dekuNukem/ATX4VC/photos/begin.png

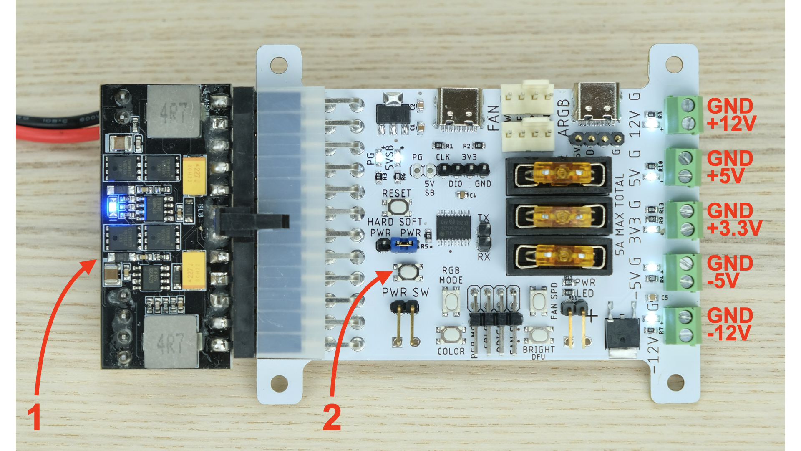
photos/begin.png
