dekuNukem/ATX4VC/photos/coffee.jpeg

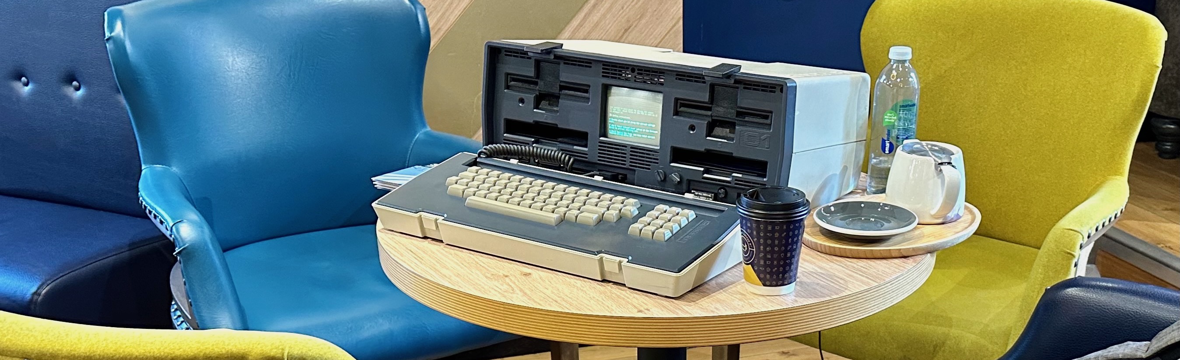
photos/coffee.jpeg
