dekuNukem/ATX4VC/photos/fuse.png

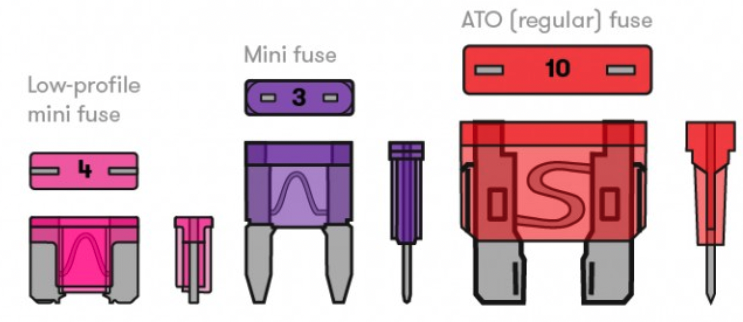
photos/fuse.png
