dekuNukem/ATX4VC/photos/fuses.jpeg

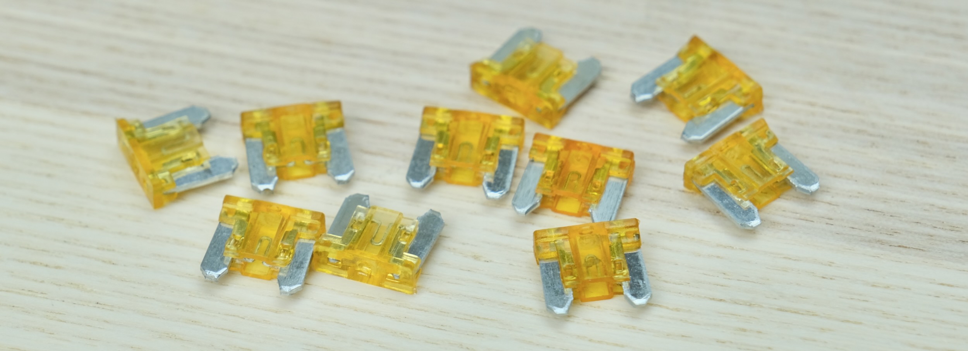
photos/fuses.jpeg
