dekuNukem/ATX4VC/photos/harness.jpeg

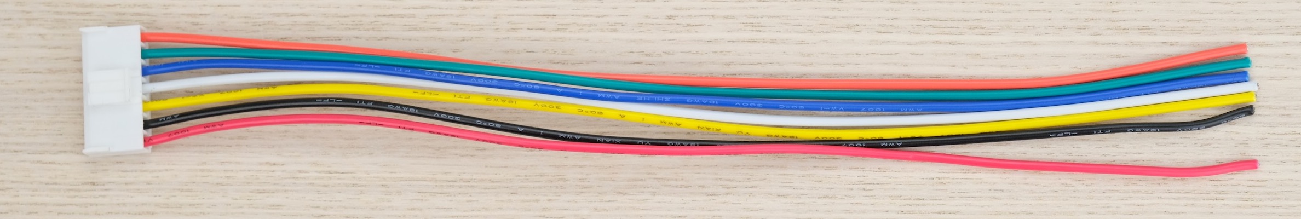
photos/harness.jpeg
