dekuNukem/ATX4VC/photos/jump.png

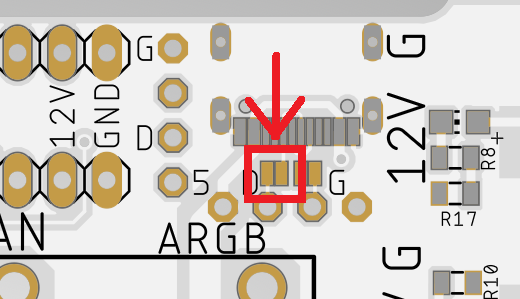
photos/jump.png
