dekuNukem/ATX4VC/photos/legend.png

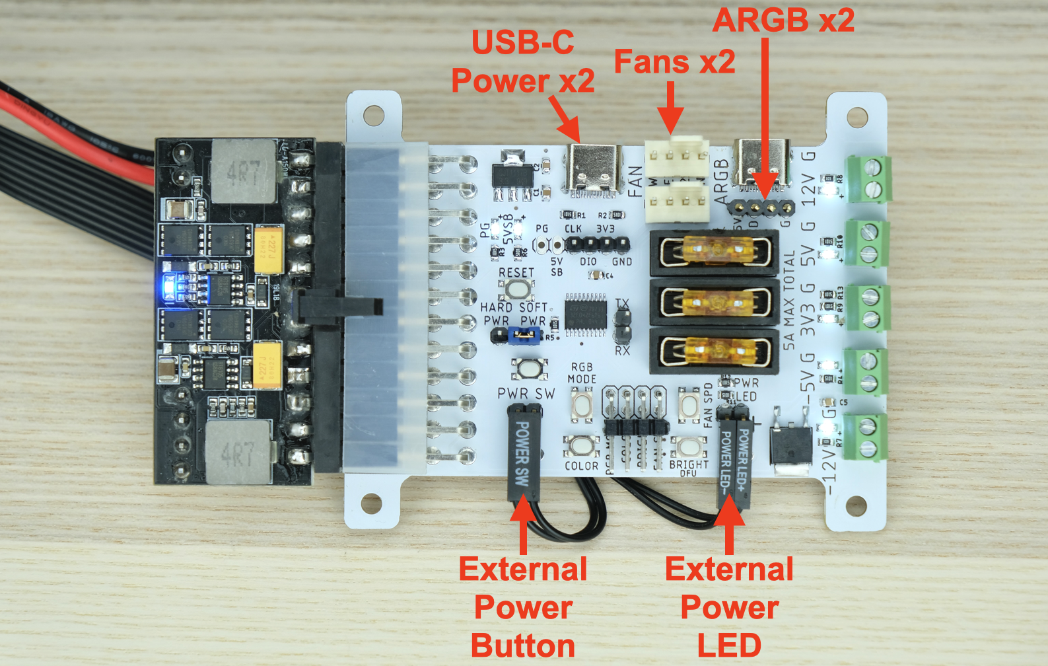
photos/legend.png
