dekuNukem/ATX4VC/photos/lock.jpeg

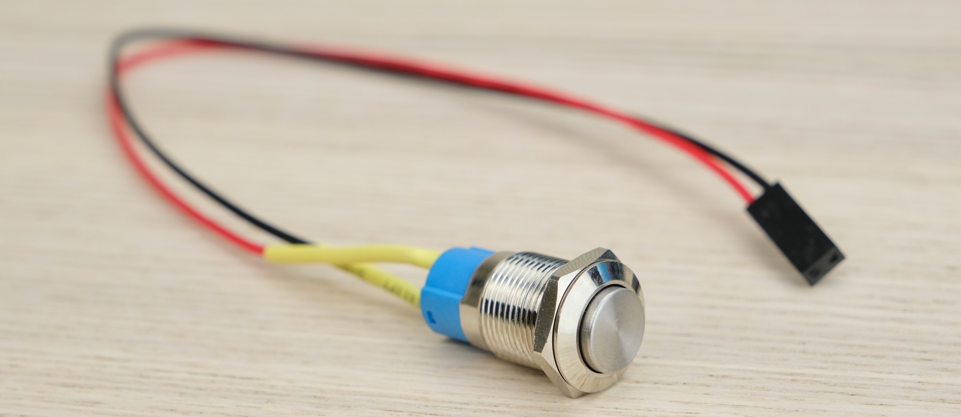
photos/lock.jpeg
