dekuNukem/ATX4VC/photos/mcu.jpeg

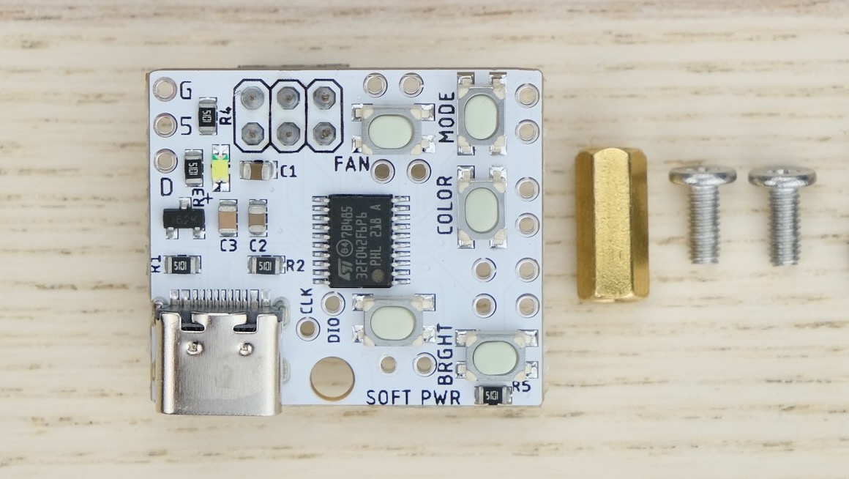
photos/mcu.jpeg
