dekuNukem/ATX4VC/photos/plug.jpeg

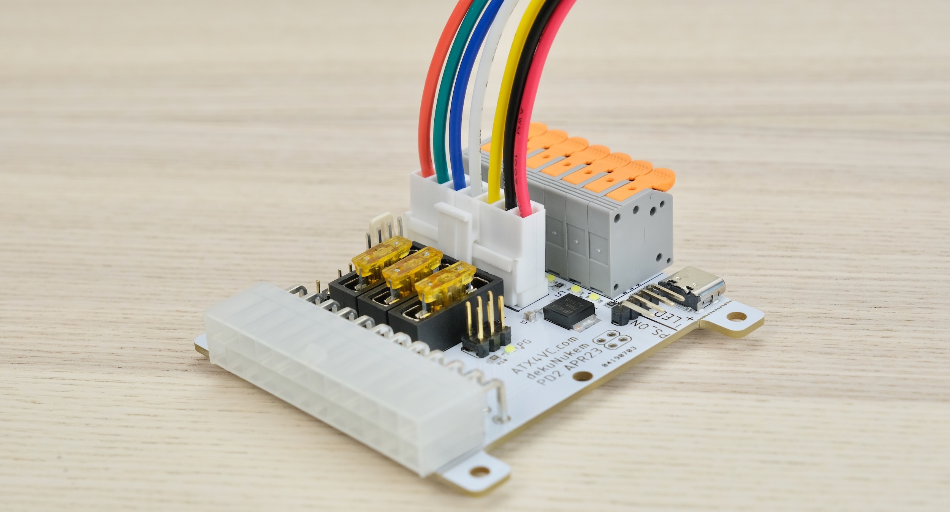
photos/plug.jpeg
