dekuNukem/ATX4VC/photos/switches.jpeg

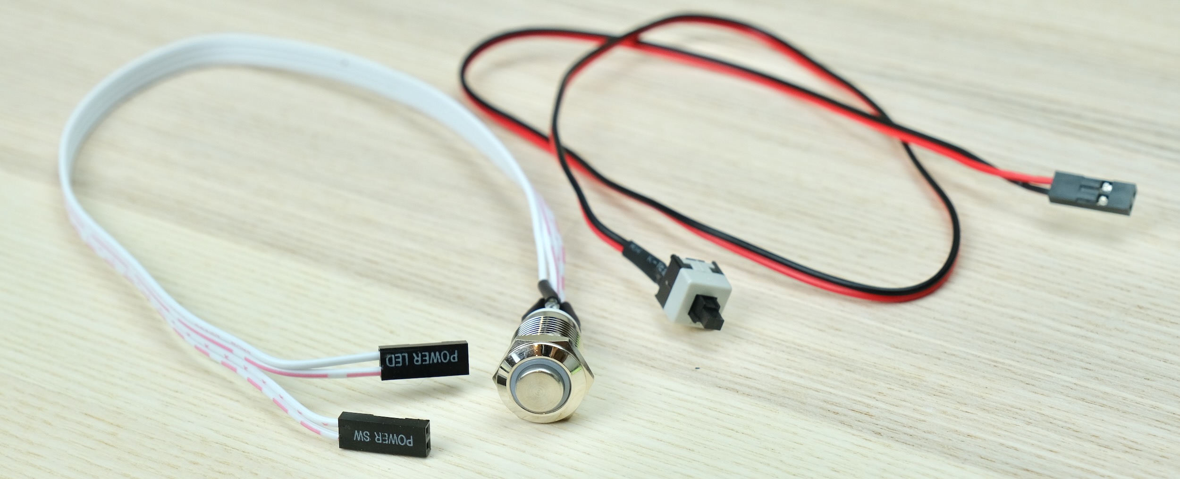
photos/switches.jpeg
