dekuNukem/ATX4VC/resources/newatx4vc.png

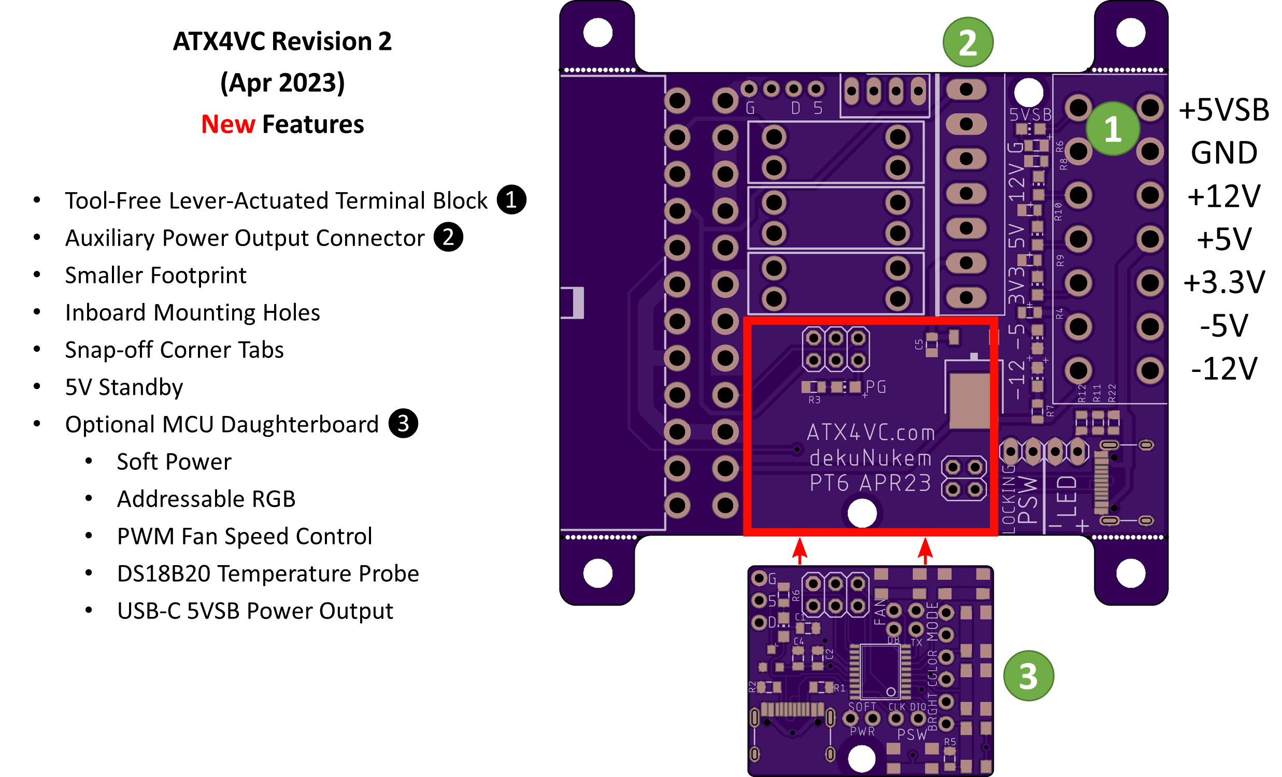
resources/newatx4vc.png
