dekuNukem/ATX4VC/resources/sparkfun_motor_driver/SparkFun_Qwiic_Motor_Driver.brd

## EAGLE design resources/sparkfun_motor_driver/SparkFun_Qwiic_Motor_Driver.brd (2022-07-18)

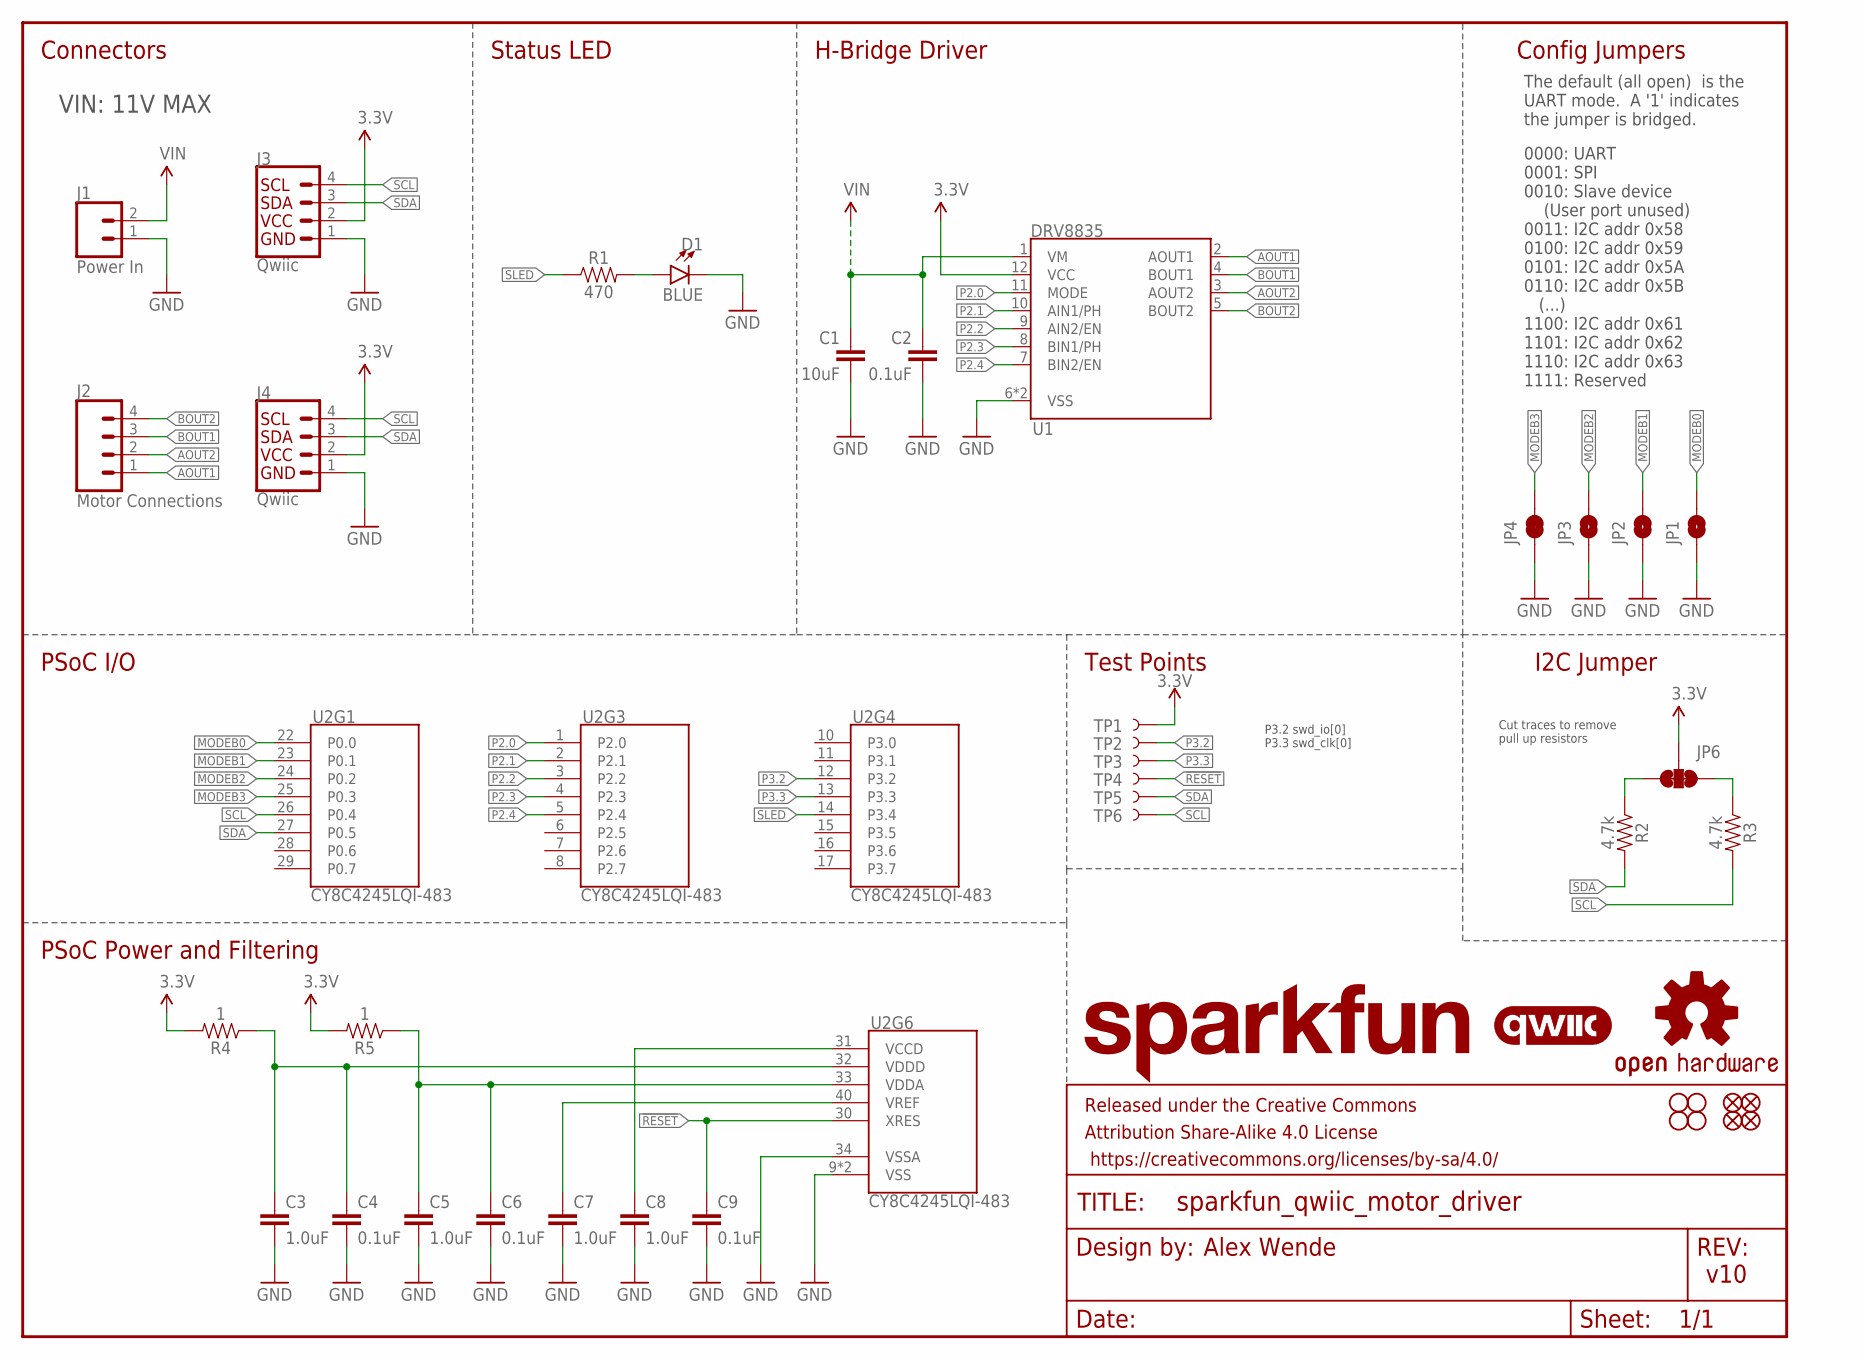
[picture p78: schematic SparkFun_Qwiic_Motor_Driver.sch]

Parts:
C1: 10uF; 0805
C2, C4, C6, C9: 0.1uF; 0402
C3, C5, C7, C8: 1.0uF; 0402
D1: BLUE; LED-0603
FD1, FD2, FD3, FD4: FIDUCIALUFIDUCIAL; FIDUCIAL-MICRO
FRAME1: FRAME-LETTER; CREATIVE_COMMONS
H1, H2, H3, H4: STAND-OFF
J1: Power In; SCREWTERMINAL-3.5MM-2
J2: Motor Connections; SCREWTERMINAL-3.5MM-4
J3, J4: Qwiic; JST04_1MM_RA
JP1, JP2, JP3: JUMPER-PAD-2; SMT-JUMPER_2_NO_NO-SILK
JP4: JUMPER-PAD-2; SMT-JUMPER_2_NC_TRACE_NO-SILK
JP6: JUMPER-SMT_3_2-NC_TRACE_NO-SILK; SMT-JUMPER_3_2-NC_TRACE_NO-SILK
LOGO2: OSHW-LOGOMINI; OSHW-LOGO-MINI
LOGO3: SFE_LOGO_NAME.1_INCH; SFE_LOGO_NAME_.1
R1: 470; 0603
R2, R3: 4.7k; 0603
R4, R5: 1; 0603
TP1, TP2, TP3, TP4, TP5, TP6: TEST-POINTTP_15TH_THRU; TP_15TH
U1: DRV8835; WSON-12
U2: CY8C4245LQI-483; QFN-40
U$1: QWIIC_LOGO_5MM; QWIIC_5MM

Connections:
3.3V: J3.2, J4.2, JP6.2, R4.2, R5.2, TP1.P$1, U1.12 (VCC)
!RESET: C9.1, TP4.P$1, U2.30 (XRES)
AOUT1: J2.1, U1.2 (AOUT1)
AOUT2: J2.2, U1.3 (AOUT2)
BOUT1: J2.3, U1.4 (BOUT1)
BOUT2: J2.4, U1.5 (BOUT2)
GND: C1.2, C2.2, C3.2, C4.2, C5.2, C6.2, C7.2, C8.2, C9.2, D1.C, J1.1, J3.1, J4.1, JP1.1, JP2.1, JP3.1, JP4.1, U1.6 (VSS), U1.PAD (VSS), U2.9 (VSS), U2.34 (VSSA), U2.EP (VSS)
MODEB0: JP1.2, U2.22 (P0.0)
MODEB1: JP2.2, U2.23 (P0.1)
MODEB2: JP3.2, U2.24 (P0.2)
MODEB3: JP4.2, U2.25 (P0.3)
unnamed: C8.1, U2.31 (VCCD)
unnamed: C5.1, C6.1, R5.1, U2.33 (VDDA)
unnamed: C7.1, U2.40 (VREF)
unnamed: D1.A, R1.2
unnamed: JP6.1, R3.1
unnamed: JP6.3, R2.1
P2.0: U1.11 (MODE), U2.1 (P2.0)
P2.1: U1.10 (AIN1/PH), U2.2 (P2.1)
P2.2: U1.9 (AIN2/EN), U2.3 (P2.2)
P2.3: U1.8 (BIN1/PH), U2.4 (P2.3)
P2.4: U1.7 (BIN2/EN), U2.5 (P2.4)
P3.2: TP2.P$1, U2.12 (P3.2)
P3.3: TP3.P$1, U2.13 (P3.3)
SCL: J3.4, J4.4, R3.2, TP6.P$1, U2.26 (P0.4)
SDA: J3.3, J4.3, R2.2, TP5.P$1, U2.27 (P0.5)
SLED: R1.1, U2.14 (P3.4)
VDDD: C3.1, C4.1, R4.1, U2.32 (VDDD)
VIN: C1.1, C2.1, J1.2, U1.1 (VM)

Notes on the sheet:
PSoC Power and Filtering
Config Jumpers
Alex Wende
PSoC I/O
v10
P3.2 swd_io[0] P3.3 swd_clk[0]
0000: UART 0001: SPI 0010: Slave device (User port unused) 0011: I2C addr 0x58 0100: I2C addr 0x59 0101: I2C addr 0x5A 0110: I2C addr 0x5B (...) 1100: I2C addr 0x61 1101: I2C addr 0x62 1110: I2C addr 0x63 1111: Reserved
The default (all open) is the UART mode. A '1' indicates the jumper is bridged.
Connectors
Status LED
H-Bridge Driver
Test Points
I2C Jumper
VIN: 11V MAX
Cut traces to remove pull up resistors

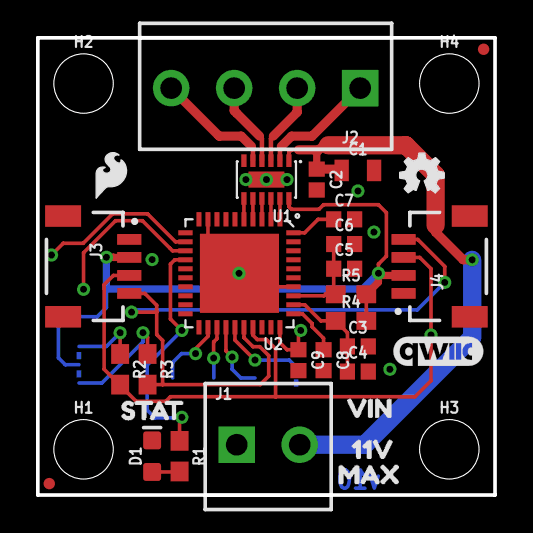
[picture p79: board SparkFun_Qwiic_Motor_Driver.brd from above]

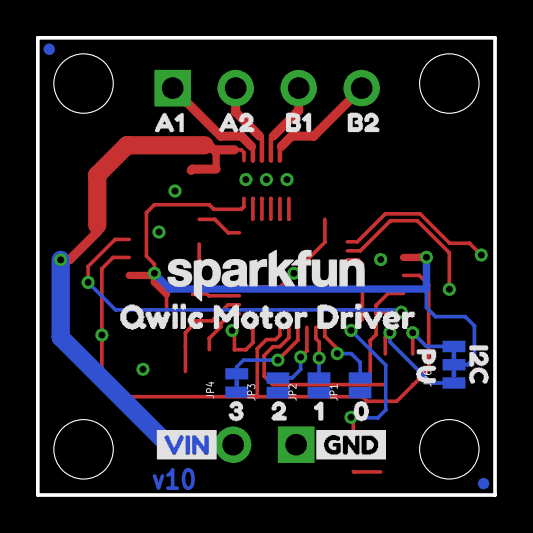
[picture p80: board SparkFun_Qwiic_Motor_Driver.brd from below]

Board: 2 copper layers, 25.4 x 25.4 mm, 62 parts (21 on the bottom side), 29 nets.

Other parts of the board:
U$2: STAT4
U$3: GND3
U$4: VIN2
U$5: 05
U$6: 16
U$7: 27
U$8: 38
U$9: A110
U$10: A211
U$11: B112
U$12: B213
U$13: 11V7
U$14: MAX8
U$15: VIN6
U$16: I2C0
U$17: PU1
U$18: QWIIC_MOTOR_DRIVER0
U$19: SFE_LOGO_FLAME_.1
