dekuNukem/ATX4VC/resources/sparkfun_atx/Benchtop Power Supply-v13.brd

## EAGLE design resources/sparkfun_atx/Benchtop Power Supply-v13.brd (2022-07-18)

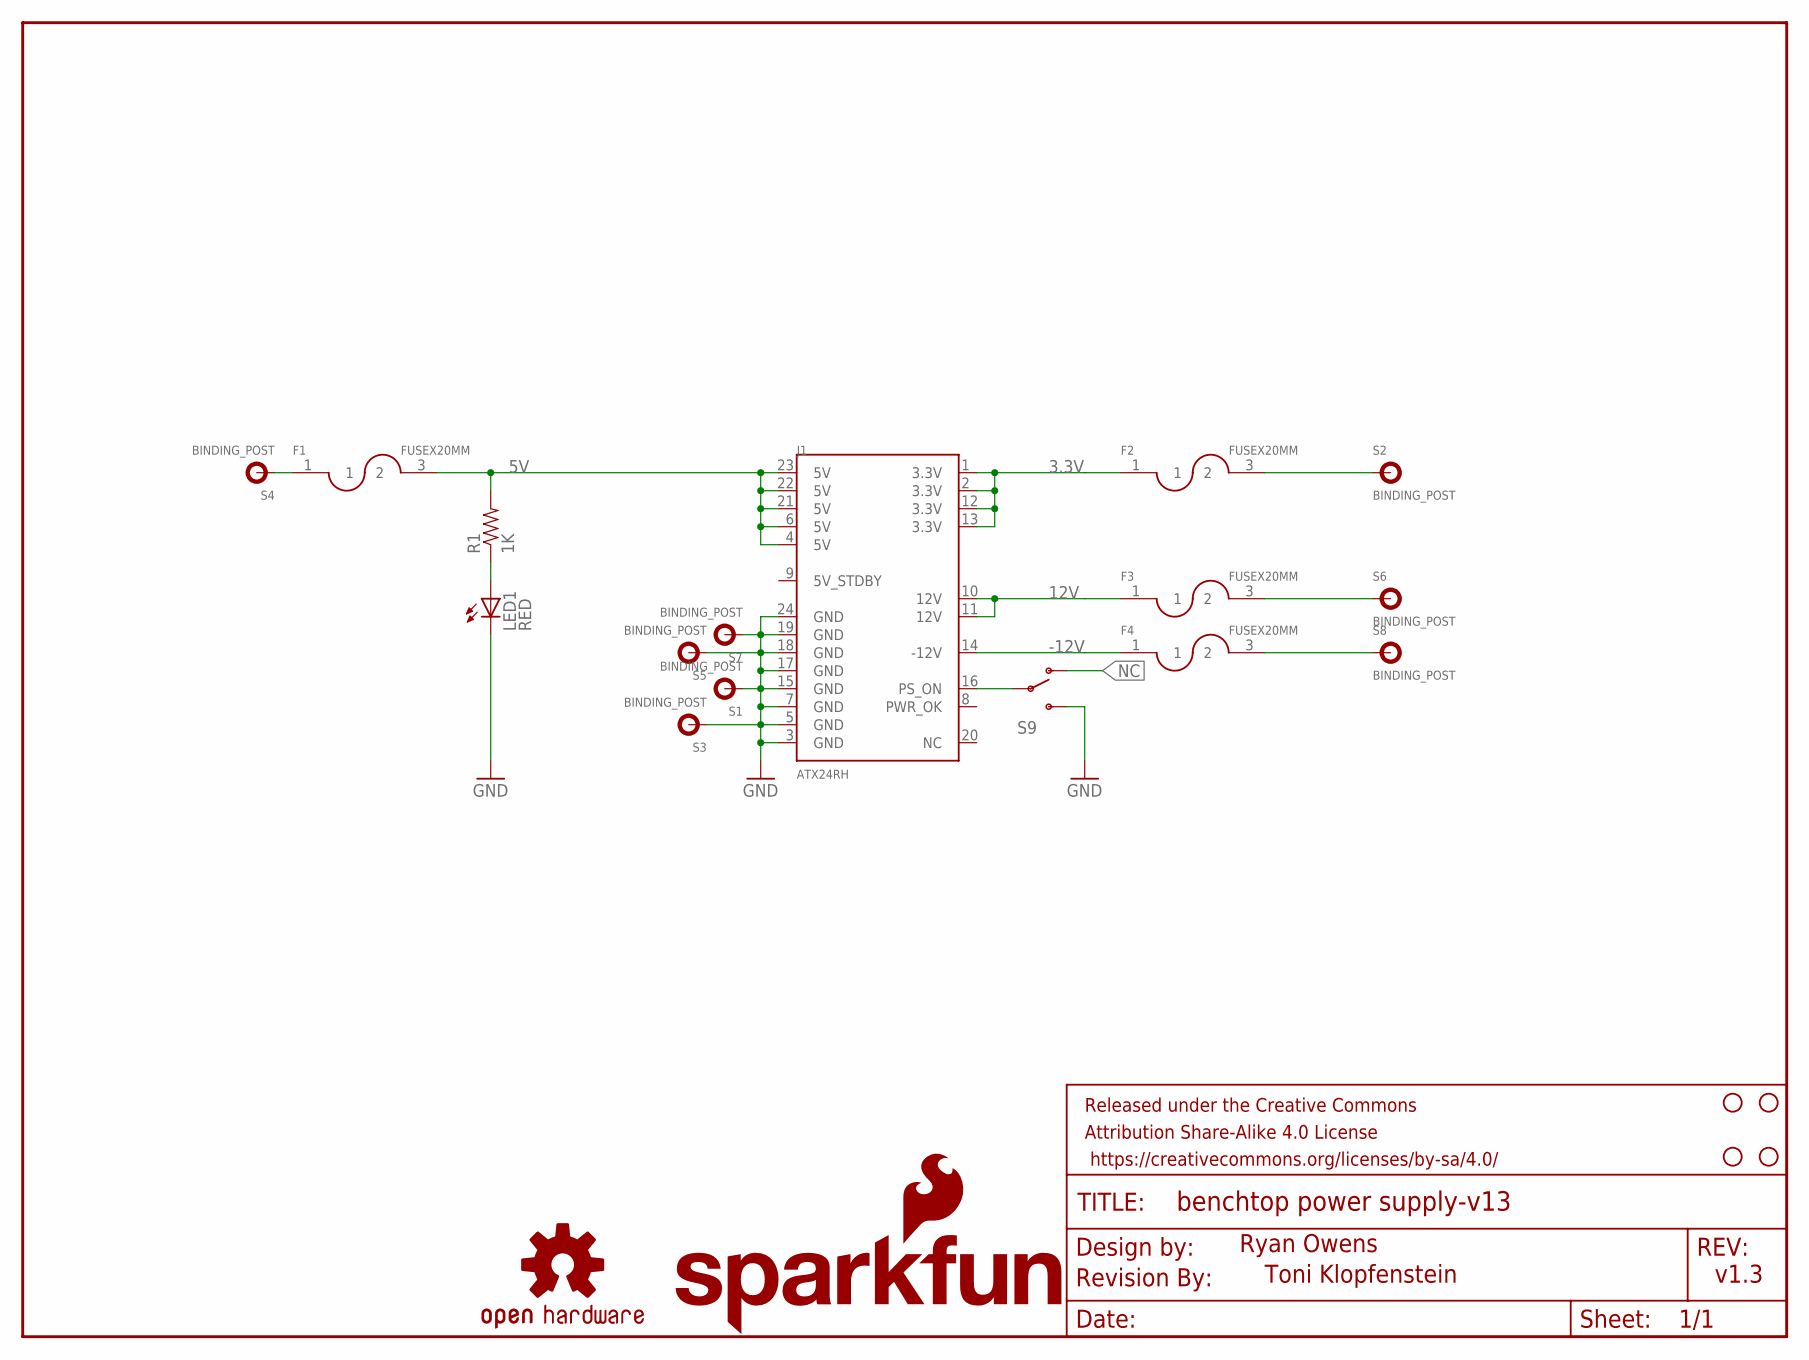
[picture p81: schematic Benchtop Power Supply-v13.sch]

Parts:
F1, F2, F3, F4: FUSEX20MM; FUSE_5MM
FRAME1: FRAME-LETTER; CREATIVE_COMMONS
J1: ATX24RH; ATX24_RIGHT_ANGLE
JP1: SFE_LOGO_NAME_FLAME.3_INCH; SFE_LOGO_NAME_FLAME_.3
JP2, JP3, JP4, JP5: STAND-OFF
LED1: RED; LED5MM
LOGO1: OSHW-LOGOL; OSHW-LOGO-L
R1: 1K; AXIAL-0.3
S1, S2, S3, S4, S5, S6, S7, S8: BINDING_POST
S9: SWITCH-SPDTKIT; SWITCH-SPDT_KIT
U$1: REVISION

Connections:
3.3V: F2.1, J1.1 (3.3V), J1.2 (3.3V), J1.12 (3.3V), J1.13 (3.3V)
3.3V_P: F2.3 (2), S2.P$1
5V: F1.3 (2), J1.4 (5V), J1.6 (5V), J1.21 (5V), J1.22 (5V), J1.23 (5V), R1.P$2 (2)
5V_P: F1.1, S4.P$1
12V: F3.1, J1.10 (12V), J1.11 (12V)
12V_P: F3.3 (2), S6.P$1
-12V: F4.1, J1.14 (-12V)
-12V_P: F4.3 (2), S8.P$1
GND: J1.3 (GND), J1.5 (GND), J1.7 (GND), J1.15 (GND), J1.17 (GND), J1.18 (GND), J1.19 (GND), J1.24 (GND), LED1.K (C), S1.P$1, S3.P$1, S5.P$1, S7.P$1, S9.3 (S)
unnamed: LED1.A, R1.P$1 (1)
unnamed: J1.16 (PS_ON), S9.2
NC: S9.1 (O)

Notes on the sheet:
Ryan Owens
Toni Klopfenstein
v1.3

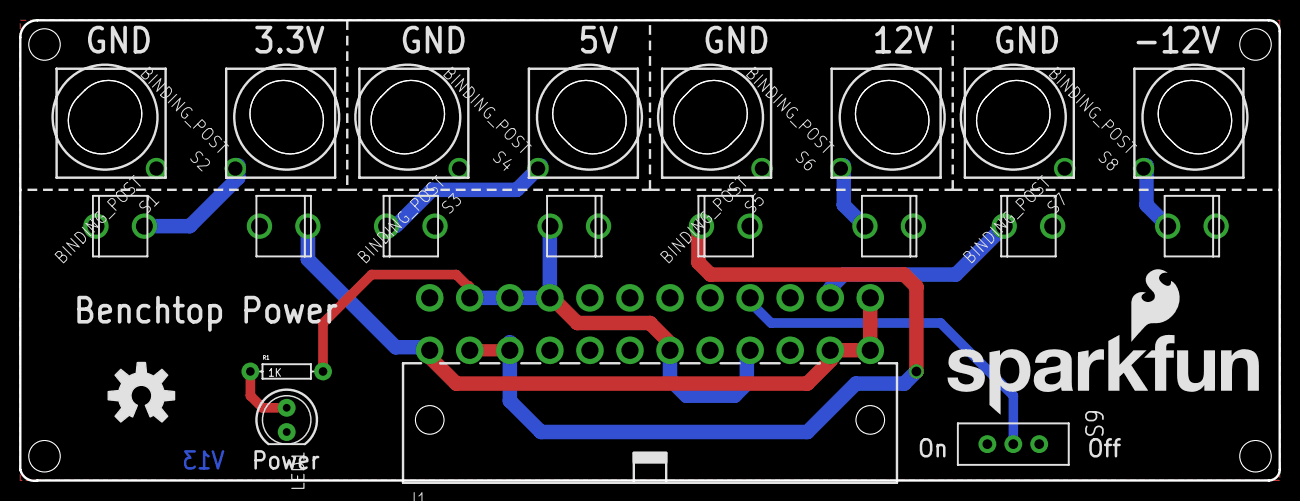
[picture p82: board Benchtop Power Supply-v13.brd from above]

Board: 2 copper layers, 132.1 x 48.3 mm, 24 parts (0 on the bottom side), 11 nets.
