dekuNukem/ATX4VC/firmware/code/Inc/neopixel.h

#ifndef __NEOPIXEL_H
#define __NEOPIXEL_H

#ifdef __cplusplus
 extern "C" {
#endif 

#include "stm32f0xx_hal.h"

#define NEOPIXEL_PADDING_BUF_SIZE 4
#define NEOPIXEL_COUNT 100
// 162
#define WS_SPI_BUF_SIZE 24
#define WS_BIT_0 0xc0
#define WS_BIT_1 0xf8

void neopixel_show(uint8_t* red, uint8_t* green, uint8_t* blue);

#ifdef __cplusplus
}
#endif

#endif
