dekuNukem/ATX4VC/firmware/code/Inc/ee.h

#ifndef __EEPROM_H
#define __EEPROM_H

/*
  Author:     Nima Askari
  WebSite:    http://www.github.com/NimaLTD
  Instagram:  http://instagram.com/github.NimaLTD
  Youtube:    https://www.youtube.com/channel/UCUhY7qY1klJm1d2kulr9ckw
  
  Version:    2.0.1
  
  (2.0.1)
  Change function name to ee_commit().
  
  Reversion History:
  (2.0.0)
  Rewrite again.

*/

#ifdef __cplusplus
 extern "C" {
#endif

#include <stdint.h>

//################################################################################################################
uint8_t      ee_format(void);
uint8_t      ee_read(uint32_t startVirtualAddress, uint32_t len, uint8_t* data);
uint8_t      ee_write(uint32_t startVirtualAddress, uint32_t len, uint8_t* data);
uint32_t  ee_maxVirtualAddress(void);

//################################################################################################################

#define   _EE_USE_FLASH_PAGE_OR_SECTOR              (31)
#define   _EE_VOLTAGE                               FLASH_VOLTAGE_RANGE_3 //  use in some devices

#ifdef __cplusplus
}
#endif

#endif
